LouisVizard/NavBoard/3D_Models/RFX2401C.stp

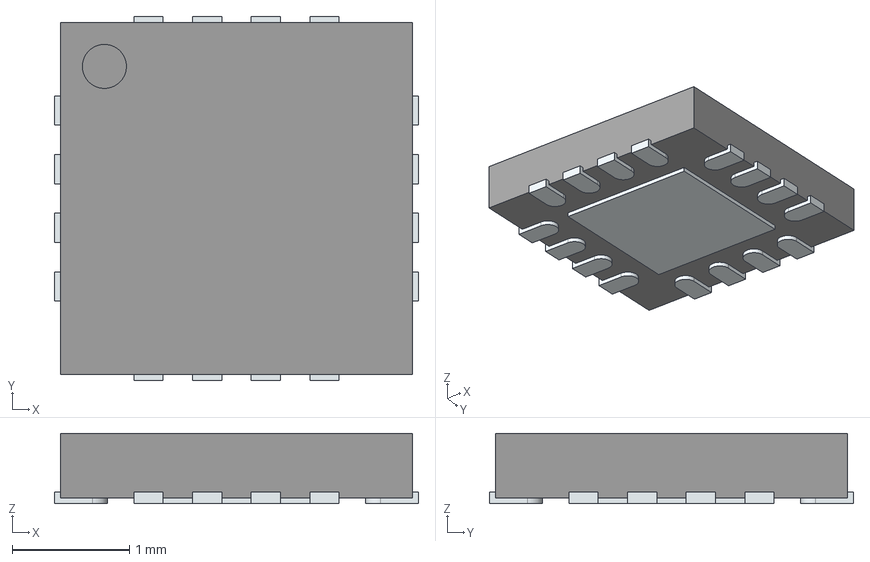
[picture p15: CAD file, 2026-06-06]
3D_Models/RFX2401C.stp
3.10 x 3.10 x 0.6 mm
ThermalPin
PinsArrayLR
PinsArrayTB
