LouisVizard/NavBoard/3D_Models/S2B-ZR_LF__SN_.stp

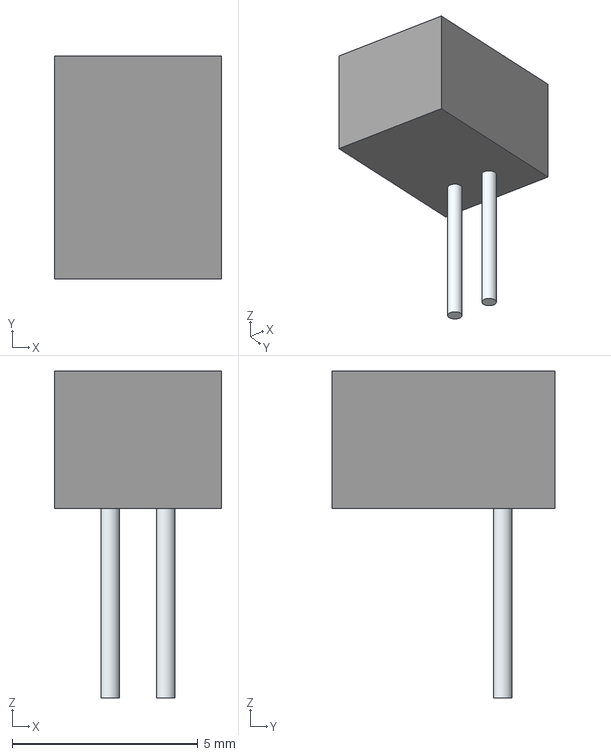
[picture p16: CAD file, 2026-06-06]
3D_Models/S2B-ZR_LF__SN_.stp
4.50 x 6.00 x 8.80 mm
Leads
