LouisVizard/NavBoard/3D_Models/SM04B-XSRS-ETB_LF__SN_.stp

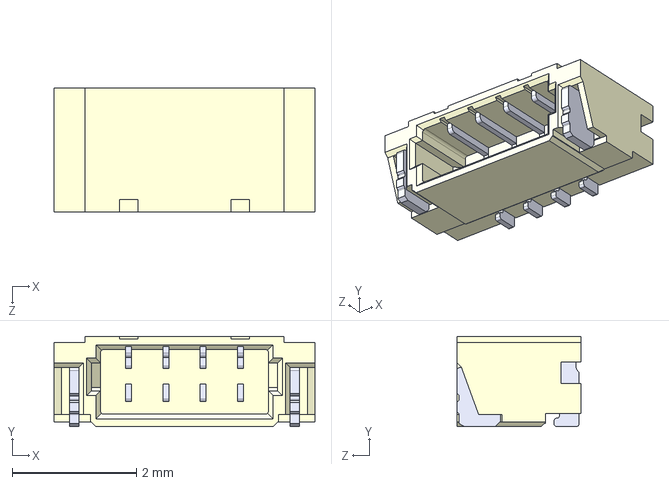
[picture p17: CAD file, 2026-06-06]
3D_Models/SM04B-XSRS-ETB_LF__SN_.stp
4.20 x 1.45 x 2.00 mm
