LouisVizard/NavBoard/3D_Models/PTS636SM43JSMTR_LFS.stp

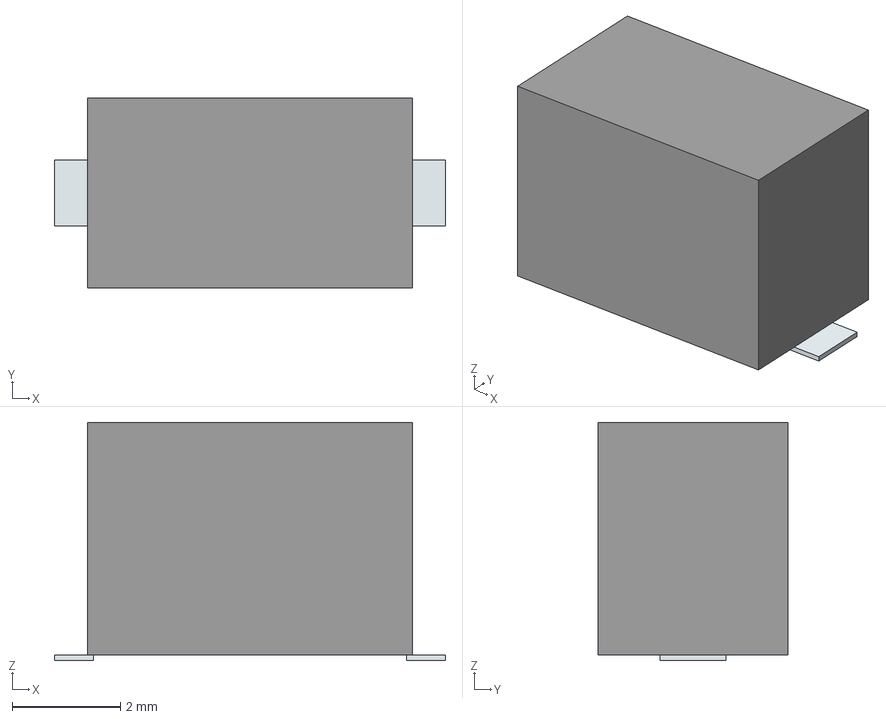
[picture p18: CAD file, 2026-06-06]
3D_Models/PTS636SM43JSMTR_LFS.stp
7.22 x 3.50 x 4.40 mm
Pins
