LouisVizard/NavBoard/3D_Models/NEO-M9N-00B.stp

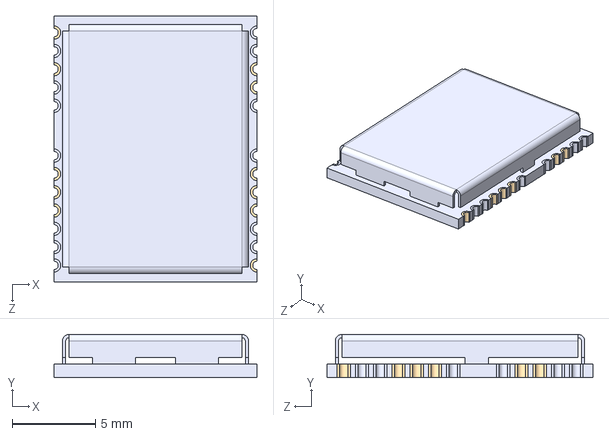
[picture p19: CAD file, 2026-06-06]
3D_Models/NEO-M9N-00B.stp
12.2 x 2.60 x 16.0 mm
