LouisVizard/NavBoard/3D_Models/CONSMA022-G.stp

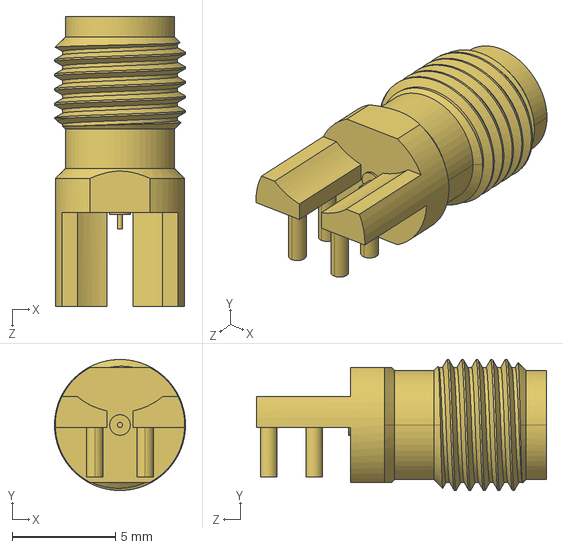
[picture p20: CAD file, 2026-06-06]
3D_Models/CONSMA022-G.stp
6.35 x 6.35 x 14.1 mm
