LouisVizard/NavBoard/3D_Models/ABS06-32.768KHZ-T.stp

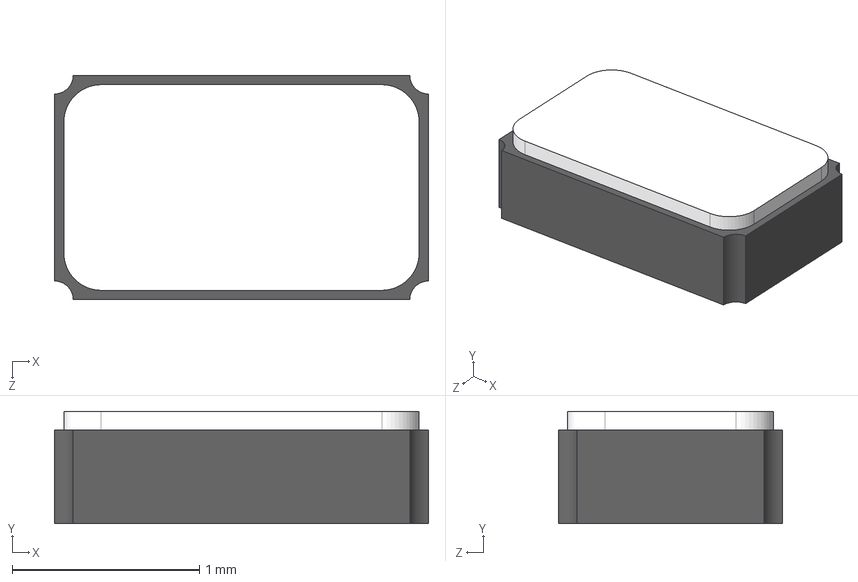
[picture p21: CAD file, 2026-06-06]
3D_Models/ABS06-32.768KHZ-T.stp
2.00 x 0.6 x 1.20 mm
