LouisVizard/NavBoard/3D_Models/XRCGB16M000FXN22R0.stp

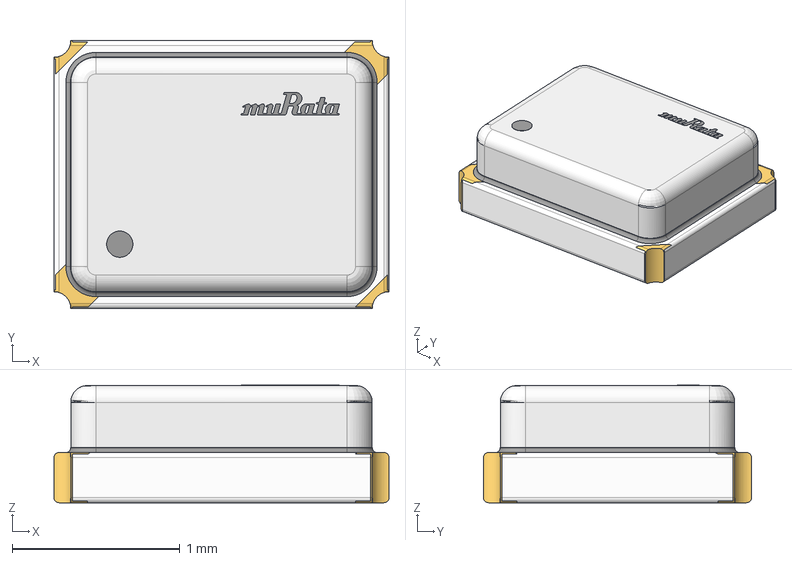
[picture p22: CAD file, 2026-06-06]
3D_Models/XRCGB16M000FXN22R0.stp
2.00 x 1.60 x 0.702 mm
