LouisVizard/NavBoard/3D_Models/S4B-ZR-SM4A-TF_LF__SN_.stp

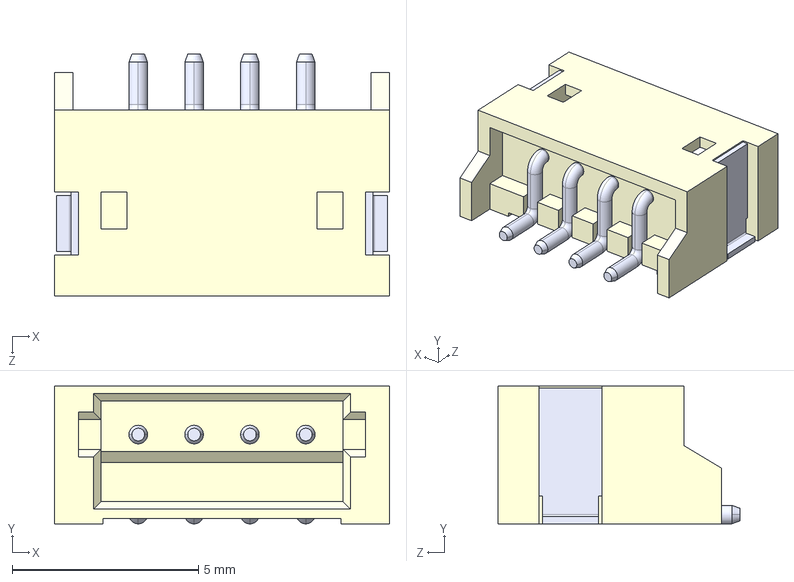
[picture p23: CAD file, 2026-06-06]
3D_Models/S4B-ZR-SM4A-TF_LF__SN_.stp
9.00 x 3.70 x 6.50 mm
