LouisVizard/NavBoard/3D_Models/S4B-ZR-3.4_LF__SN_.stp

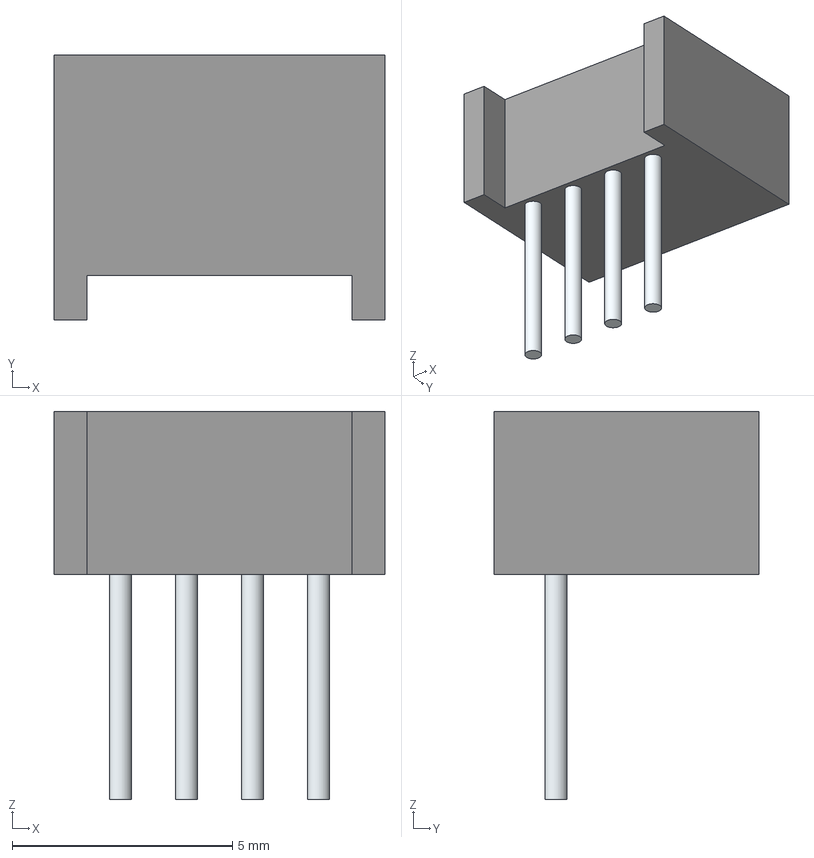
[picture p24: CAD file, 2026-06-06]
3D_Models/S4B-ZR-3.4_LF__SN_.stp
7.50 x 6.00 x 8.80 mm
Leads
