LouisVizard/NavBoard/3D_Models/PTS645VM39-2_LFS.stp

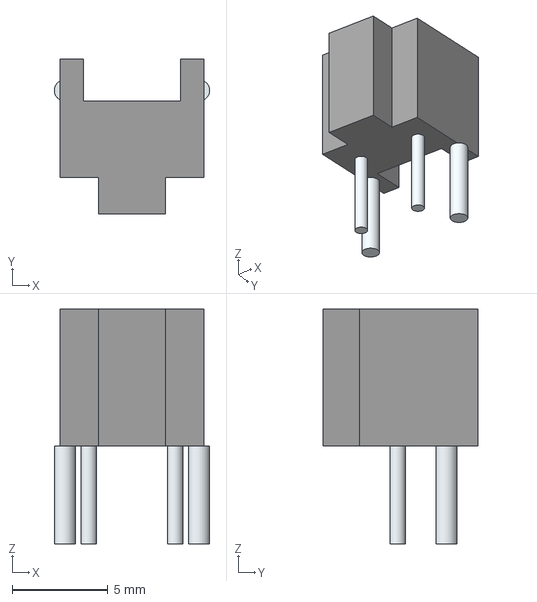
[picture p25: CAD file, 2026-06-06]
3D_Models/PTS645VM39-2_LFS.stp
8.10 x 8.10 x 12.2 mm
Leads
