LouisVizard/NavBoard/3D_Models/2450LP14A0100001T.stp

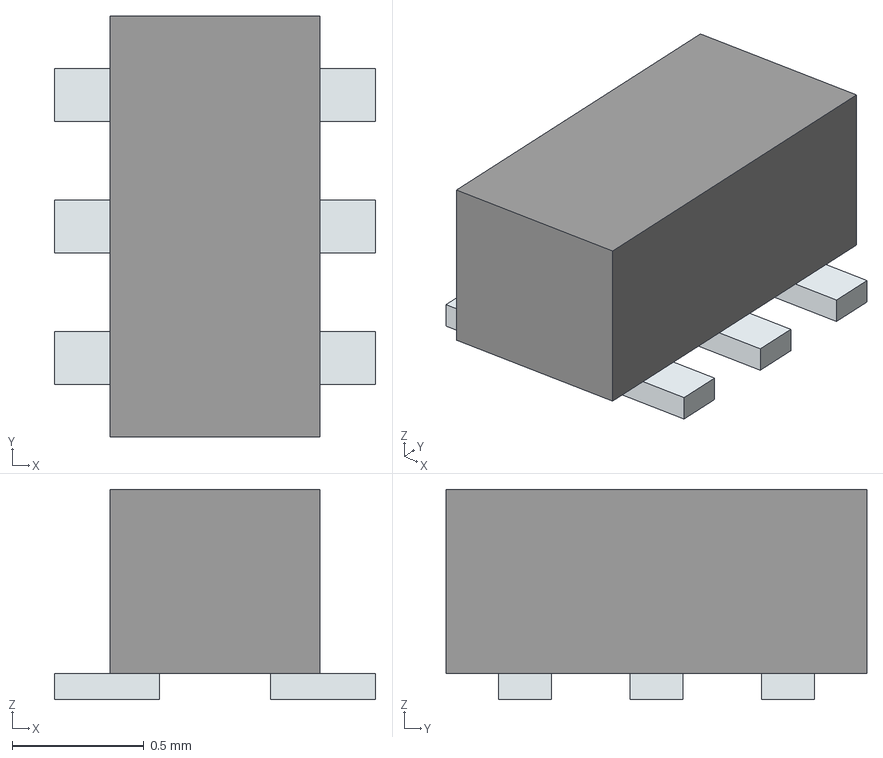
[picture p26: CAD file, 2026-06-06]
3D_Models/2450LP14A0100001T.stp
1.22 x 1.60 x 0.8 mm
Pins
